vives-project-xp/InteractiveCorridor/website/img/Pointer.png

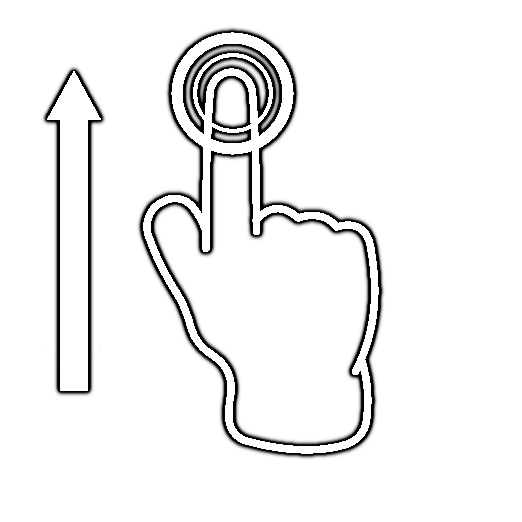
website/img/Pointer.png
